CARWHO/Halo-Vision/schematics/Brain_module/Project Outputs/3D View/3D_PCB_2024-06-09_TOP.png

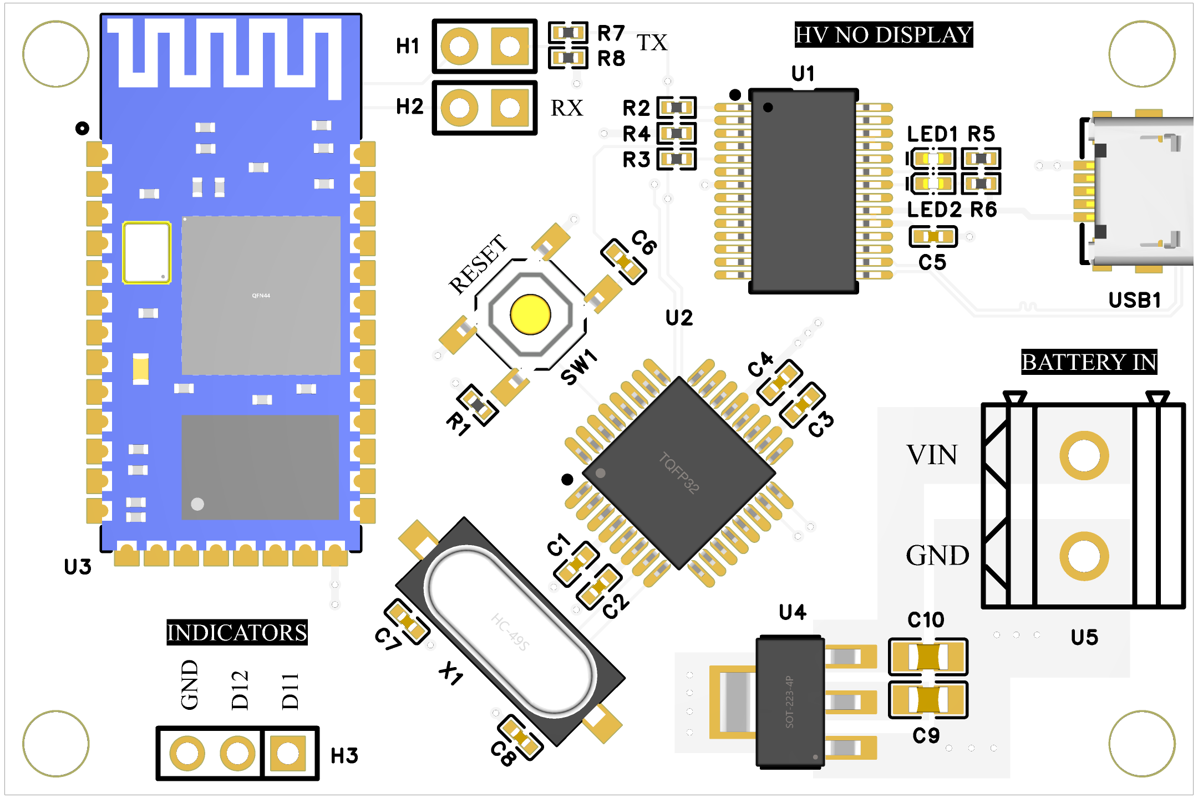
schematics/Brain_module/Project Outputs/3D View/3D_PCB_2024-06-09_TOP.png
