CARWHO/Halo-Vision/schematics/Brain_module/Project Outputs/3D View/capture-2024-06-09T12_22_44.775Z.png

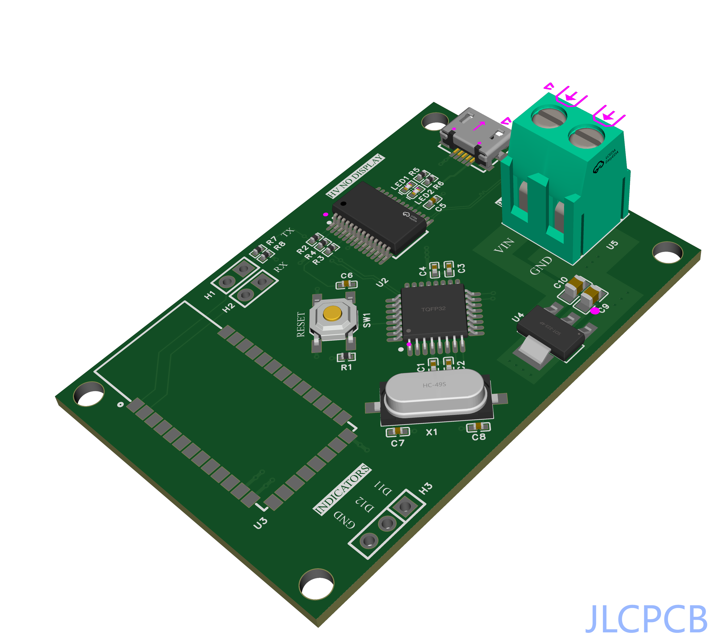
schematics/Brain_module/Project Outputs/3D View/capture-2024-06-09T12_22_44.775Z.png
