CARWHO/Halo-Vision/schematics/Display_module/Project Outputs/3D Views/3D_PCB_2024-06-08_S1.png

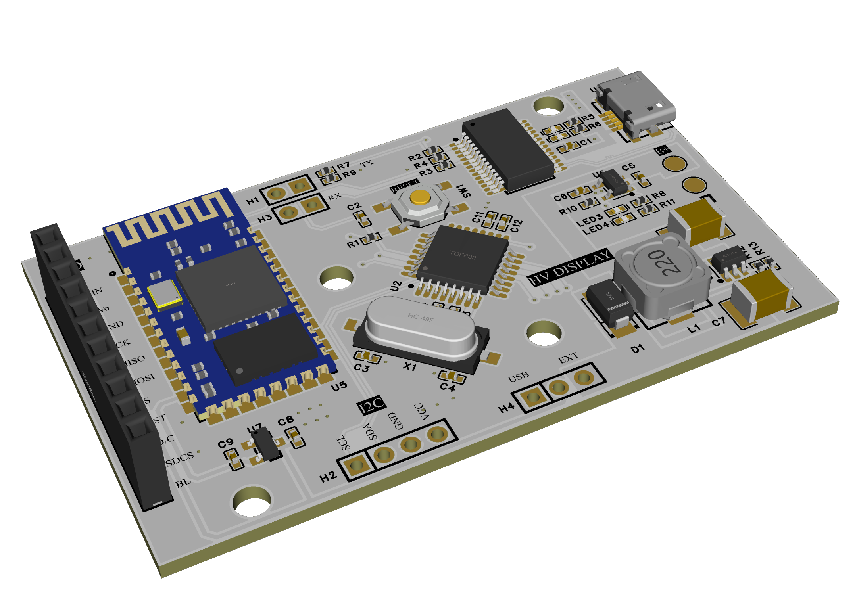
schematics/Display_module/Project Outputs/3D Views/3D_PCB_2024-06-08_S1.png
