CARWHO/Halo-Vision/schematics/Original sketches/image (6).png

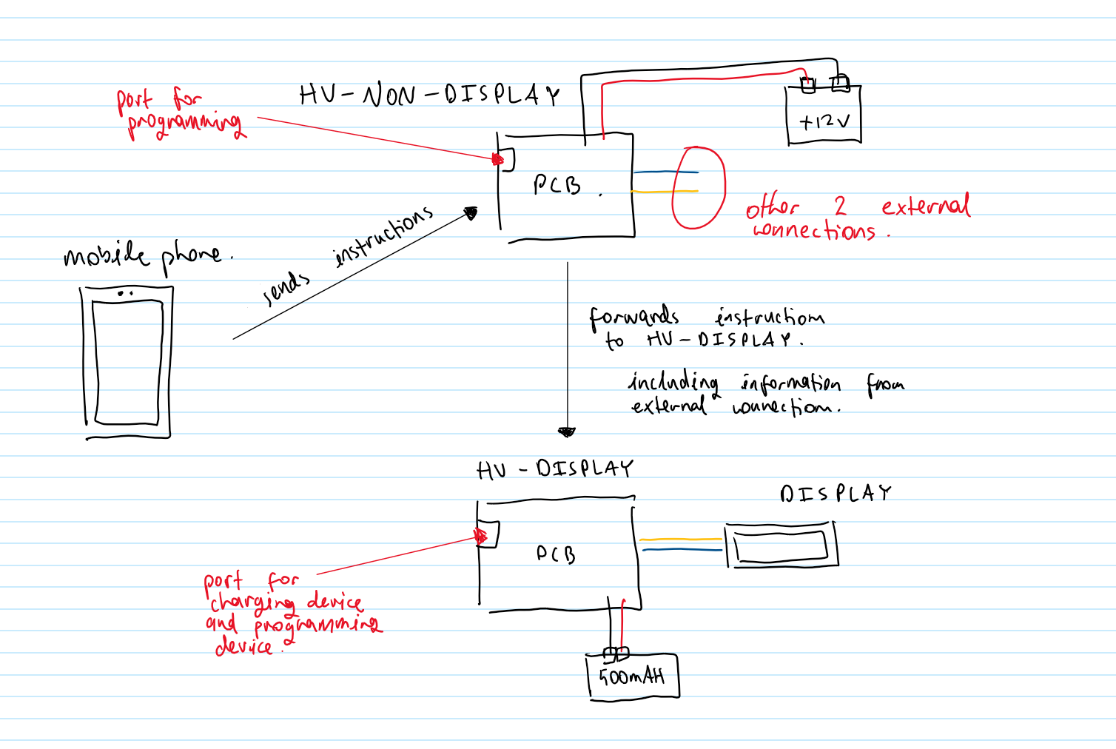
schematics/Original sketches/image (6).png
