CARWHO/Halo-Vision/schematics/Brain_module/Project Outputs/JLCPCB Quote/5 Assembled PCBS.PNG

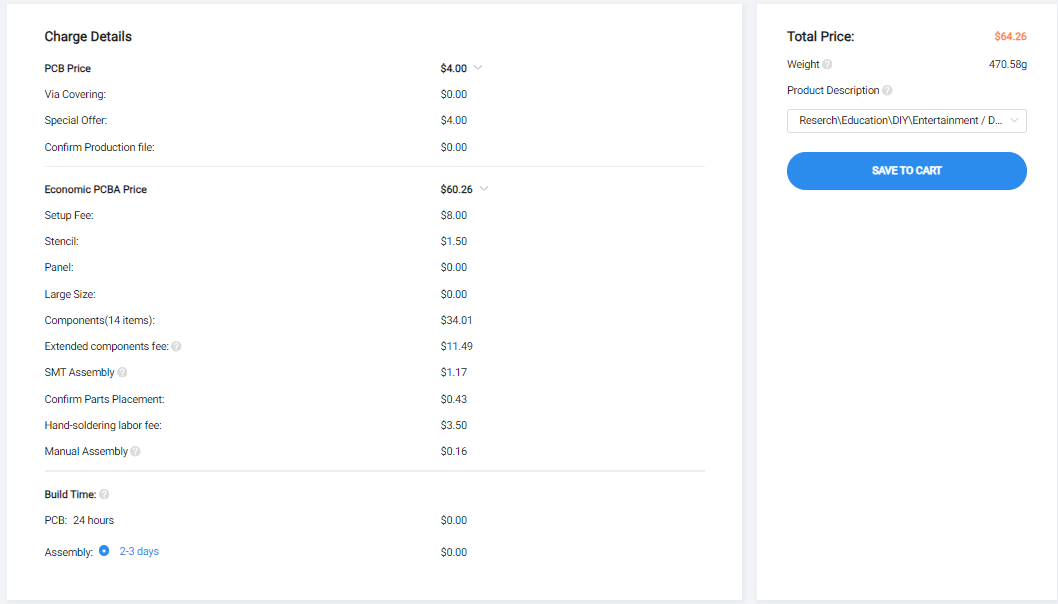
schematics/Brain_module/Project Outputs/JLCPCB Quote/5 Assembled PCBS.PNG
