CARWHO/Halo-Vision/schematics/Display_module/Project Outputs/JLCPCB Quotation/5 Assembled PCBS.PNG

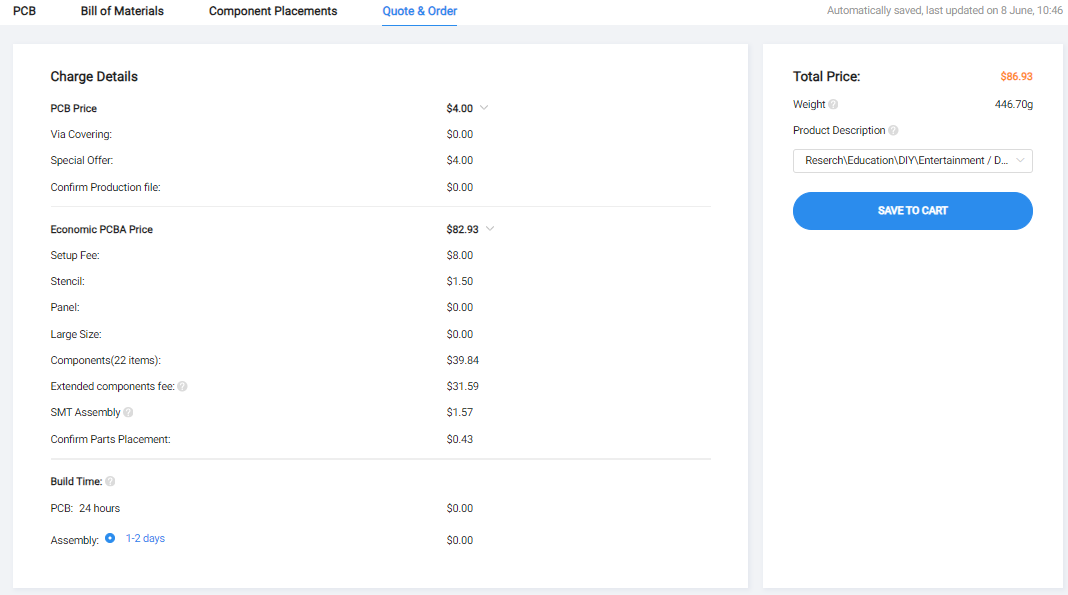
schematics/Display_module/Project Outputs/JLCPCB Quotation/5 Assembled PCBS.PNG
